konradwilk/wash-hand-pcb/v1.4-rc1/b-v1.4-rc1.png

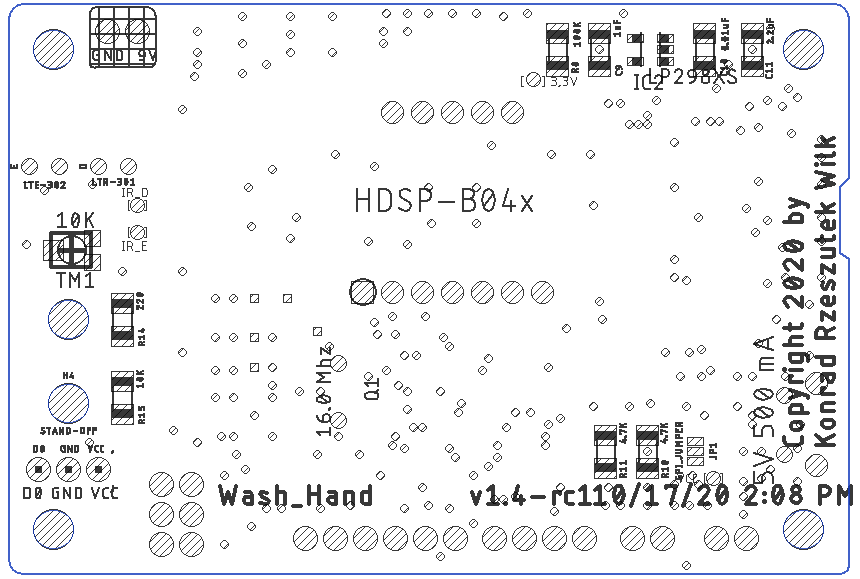
v1.4-rc1/b-v1.4-rc1.png
