konradwilk/wash-hand-pcb/v1.4-rc3/t-v1.4-rc3.png

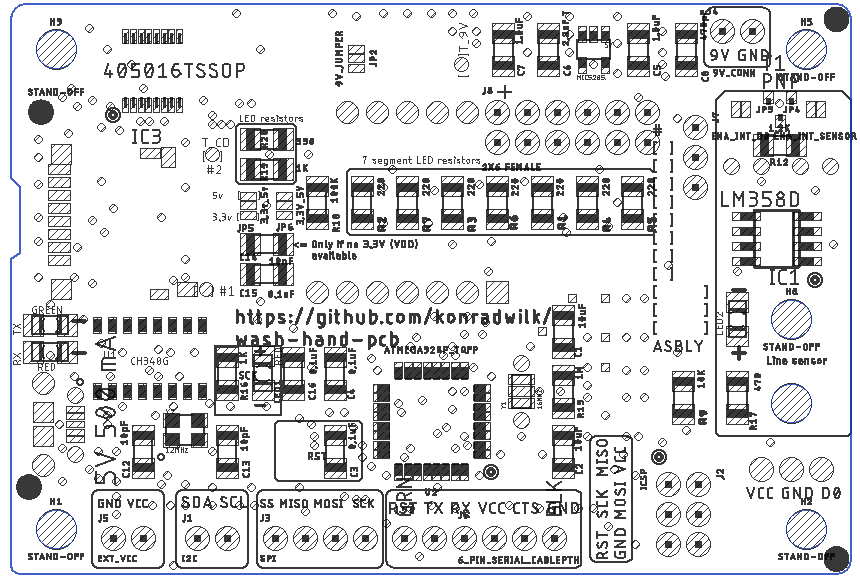
v1.4-rc3/t-v1.4-rc3.png
