konradwilk/wash-hand-pcb/v1.4-rc4/b-v1.4-rc4.png

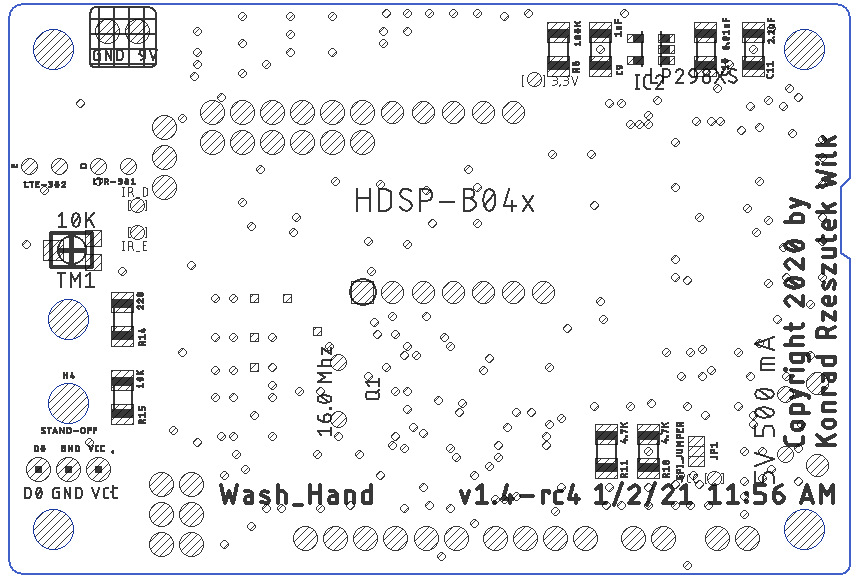
v1.4-rc4/b-v1.4-rc4.png
