konradwilk/wash-hand-pcb/v1.4-rc5/t-v1.4-rc5.png

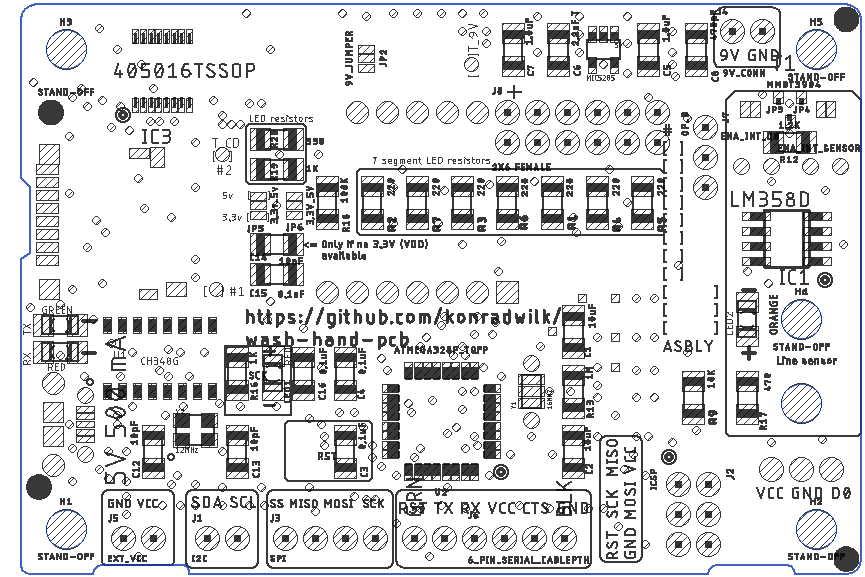
v1.4-rc5/t-v1.4-rc5.png
