konradwilk/wash-hand-pcb/Wash_Hand/v1_3.h

/*
  Copyright 2020, Konrad Rzeszutek Wilk
  SPDX-License-Identifier: CC-BY-4.0
*/

const int pinA = 2;
const int pinB = 3;
const int pinC = 4;
const int pinD = 5;
const int pinE = 6;
const int pinF = 7;
const int pinG = 8;
const int pinDP = 0; // NOT USED
const int D1 = A1;
const int D2 = A2;
const int D3 = A3;
const int D4 = 9;

unsigned int on = LOW;
unsigned int off = HIGH;

const byte BUTTON = A0;
